SilasiLab/HASRA/src/client/detection_frame.jpg

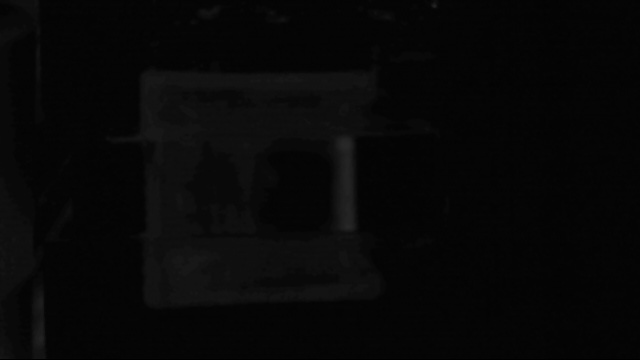
src/client/detection_frame.jpg
