SilasiLab/HASRA/resources/Images/STEP3.png

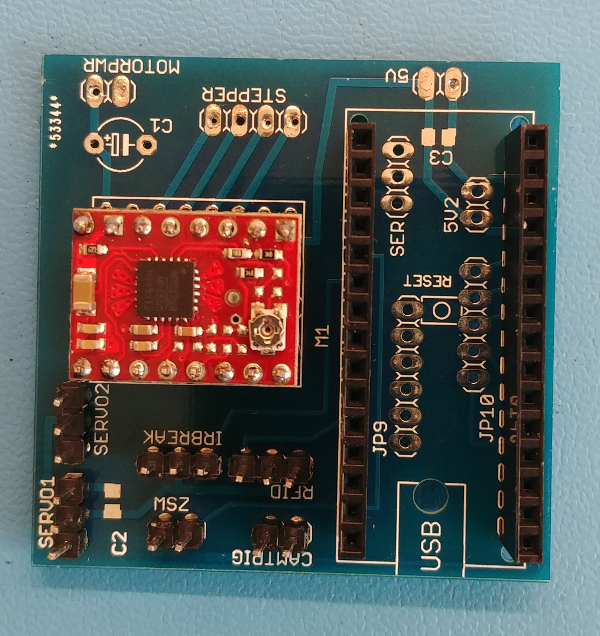
resources/Images/STEP3.png
