SilasiLab/HASRA/resources/Images/STEP5.1.png

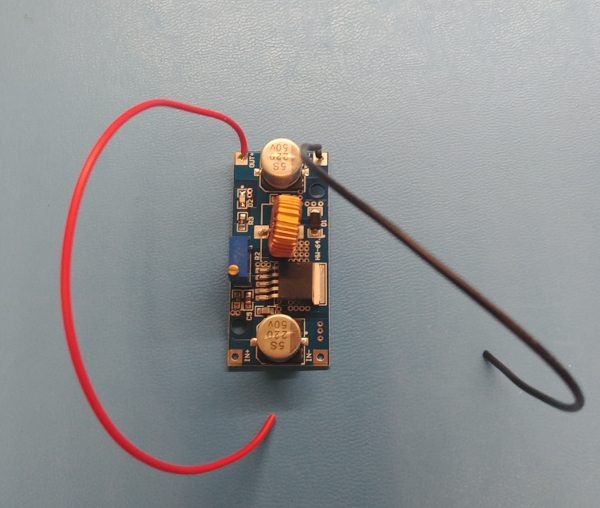
resources/Images/STEP5.1.png
