SilasiLab/HASRA/resources/Images/STEP5.2.png

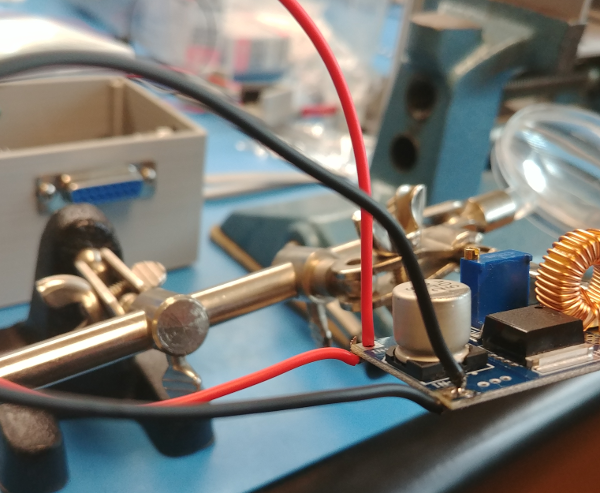
resources/Images/STEP5.2.png
