SilasiLab/HASRA/resources/Images/STEP6.png

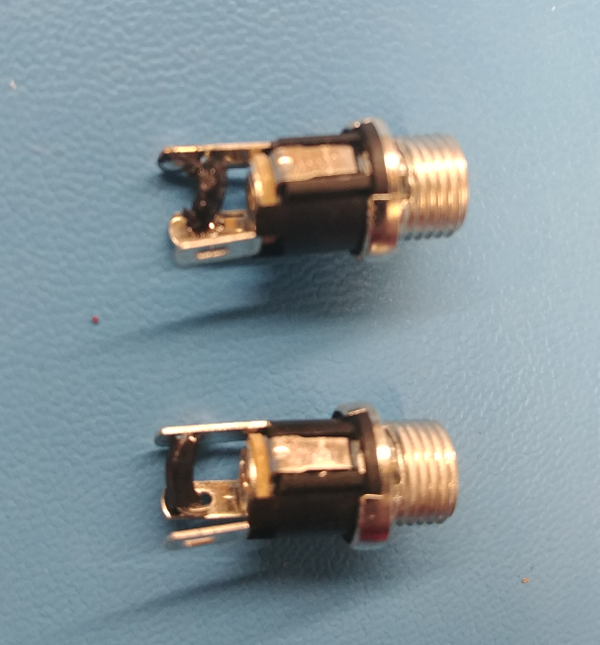
resources/Images/STEP6.png
