SilasiLab/HASRA/resources/Images/STEP7.png

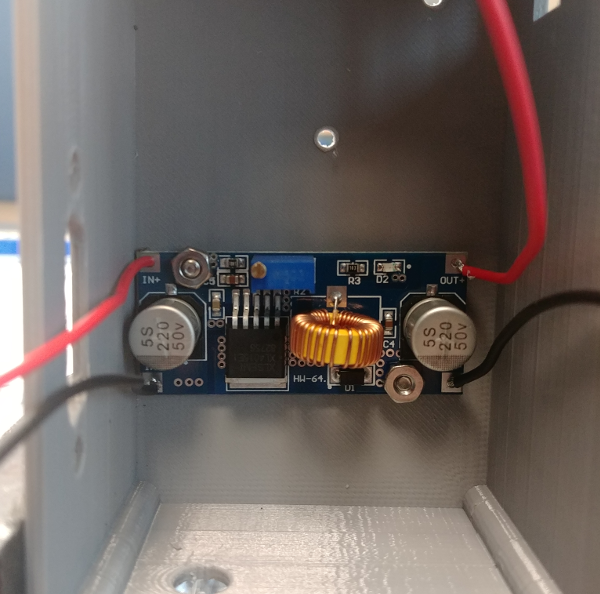
resources/Images/STEP7.png
