SilasiLab/HASRA/resources/Images/STEP8.png

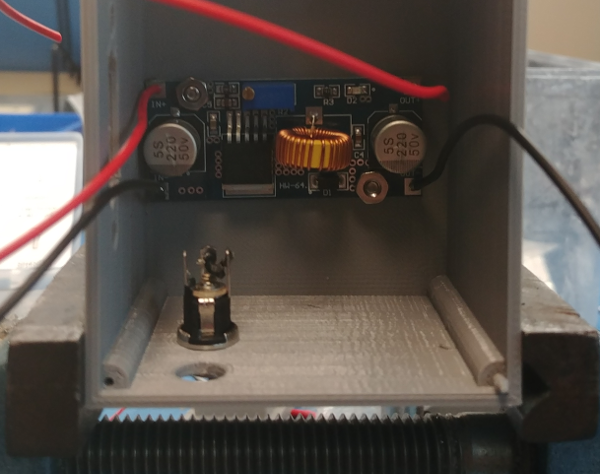
resources/Images/STEP8.png
