SilasiLab/HASRA/resources/Images/STEP9.png

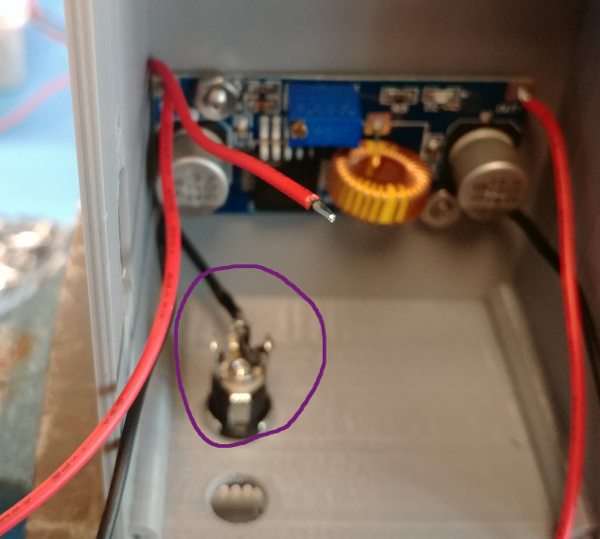
resources/Images/STEP9.png
