SilasiLab/HASRA/resources/Images/STEP11.png

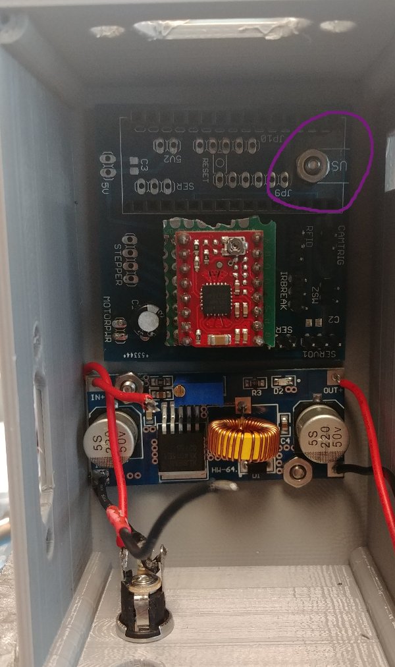
resources/Images/STEP11.png
