SilasiLab/HASRA/resources/Images/STEP17.png

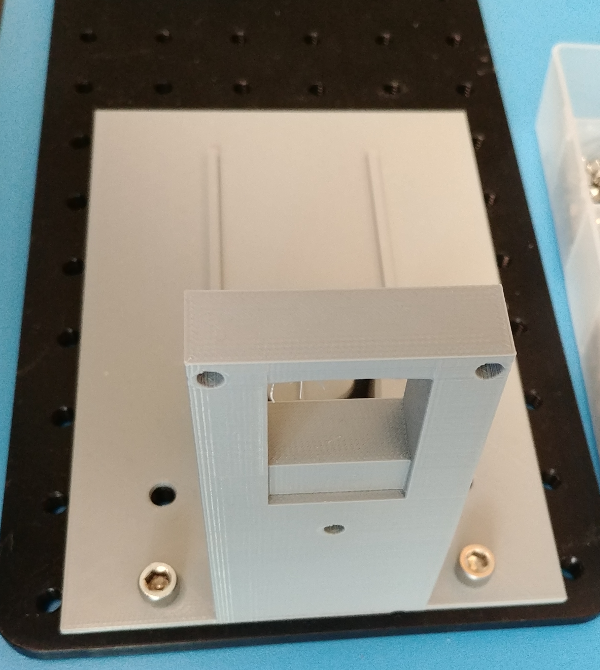
resources/Images/STEP17.png
