SilasiLab/HASRA/resources/Images/STEP18.png

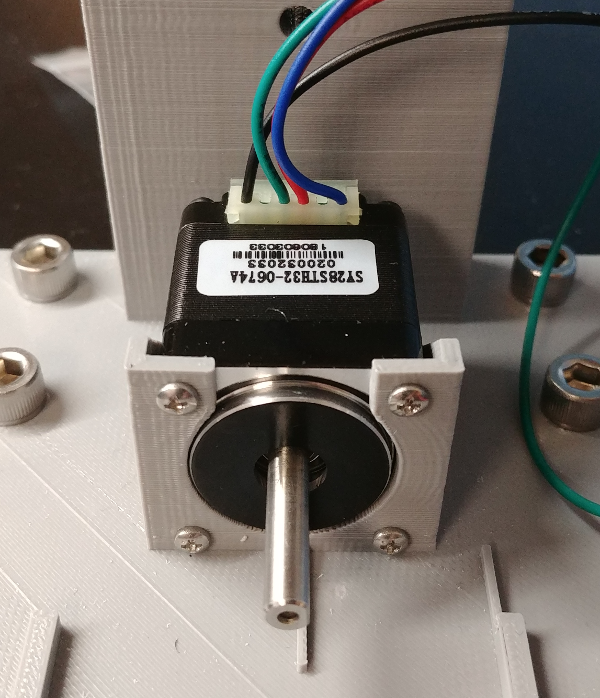
resources/Images/STEP18.png
