SilasiLab/HASRA/resources/Images/STEP21.png

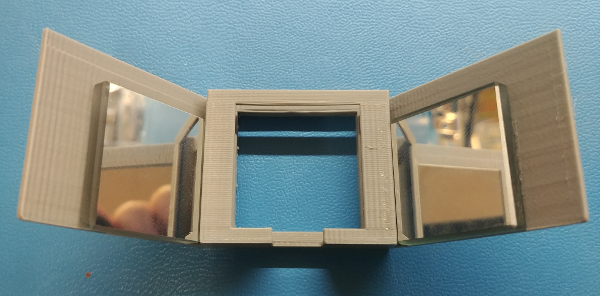
resources/Images/STEP21.png
