SilasiLab/HASRA/resources/Images/STEP24.png

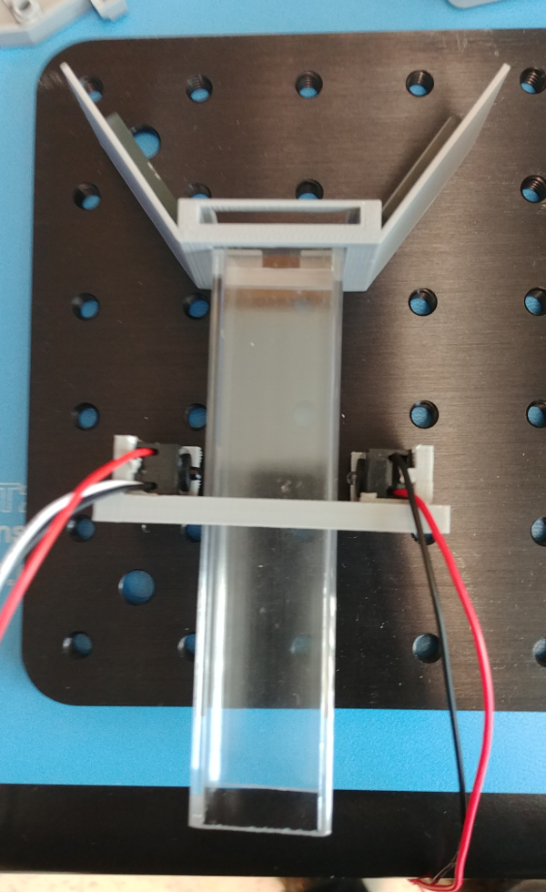
resources/Images/STEP24.png
