SilasiLab/HASRA/resources/Images/STEP25.png

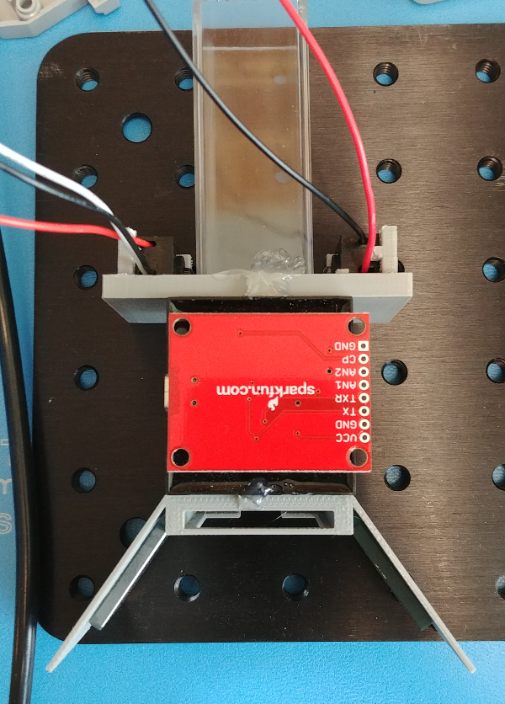
resources/Images/STEP25.png
