SilasiLab/HASRA/resources/Images/STEP26.png

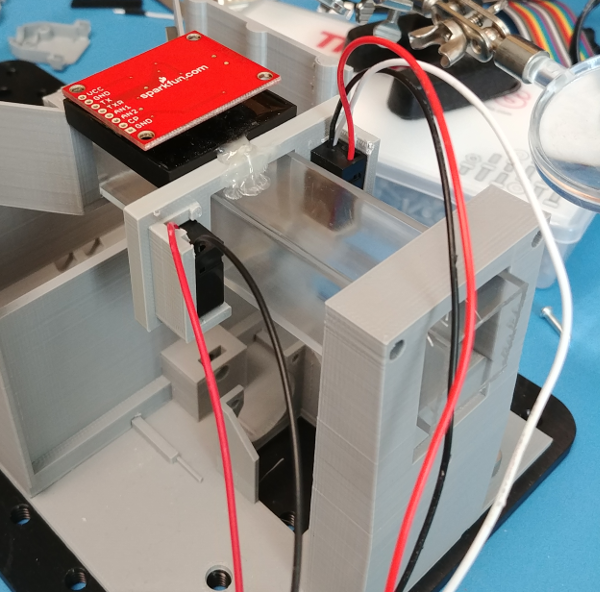
resources/Images/STEP26.png
