SilasiLab/HASRA/resources/Images/STEP27-28.png

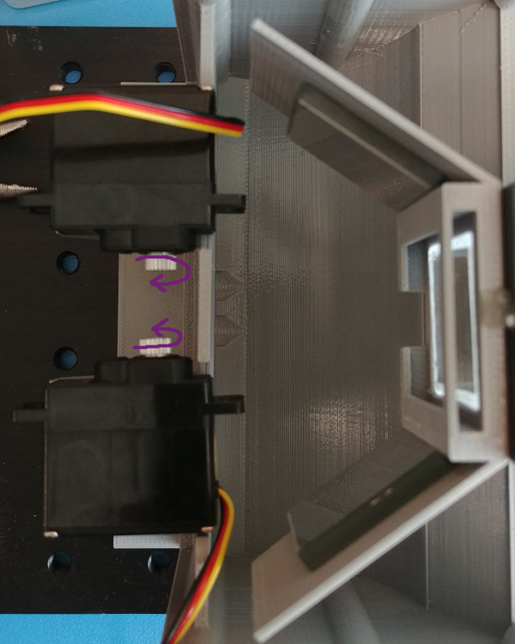
resources/Images/STEP27-28.png
