SilasiLab/HASRA/resources/Images/STEP30.png

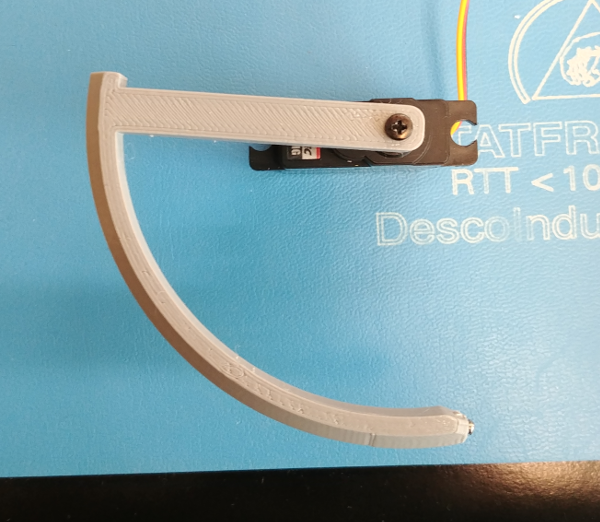
resources/Images/STEP30.png
